diyelectromusic/ESP32EduModHackThing/Hardware/ESP32EduModHackThing-Acc-panel-JST-pcb.png

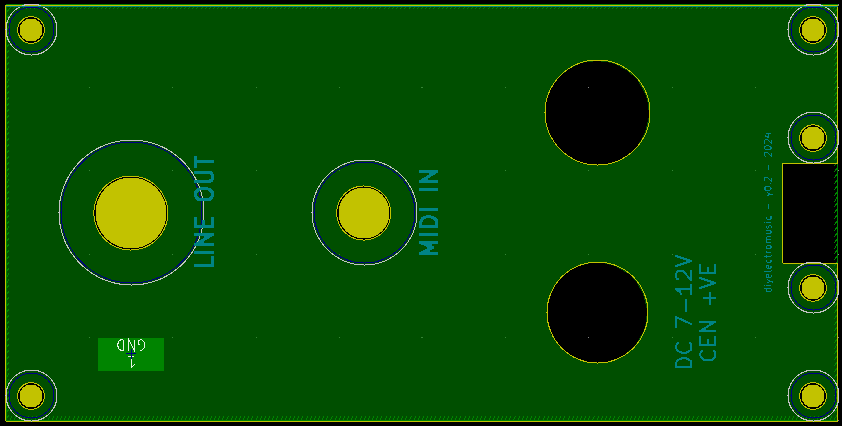
Hardware/ESP32EduModHackThing-Acc-panel-JST-pcb.png
