diyelectromusic/ESP32EduModHackThing/Hardware/ESP32EduModHackThing-Enc.png

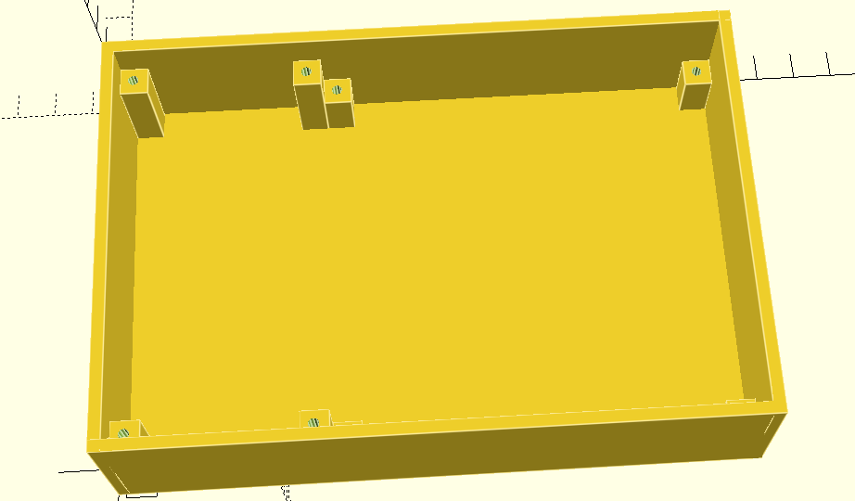
Hardware/ESP32EduModHackThing-Enc.png
