diyelectromusic/ESP32EduModHackThing/Firmware/ESP32HackModThing/midi2freq.h

#ifndef __midi2freq_include
#define __midi2freq_include

#ifdef __cplusplus
extern "C" {
#endif

static const float midi2freq[128] = {
8.18,  // MIDI Note 0
8.66,
9.18,
9.72,
10.3,
10.91,
11.56,
12.25,
12.98,
13.75,
14.57,
15.43,
16.35,
17.32,
18.35,
19.45,
20.6,
21.83,
23.12,
24.5,
25.96,
27.5,  // 21 A0
29.14,
30.87,
32.7,
34.65,
36.71,
38.89,
41.2,
43.65,
46.25,
49,
51.91,
55,        // 33 A1
58.27,
61.74,
65.41,
69.3,
73.42,
77.78,
82.41,
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
};

#ifdef __cplusplus
}
#endif
#endif
